O-V-E-R-L-O-R-D/ECE-411-Practicum/3D Model Prototype/Version 4.0/crossesction.png

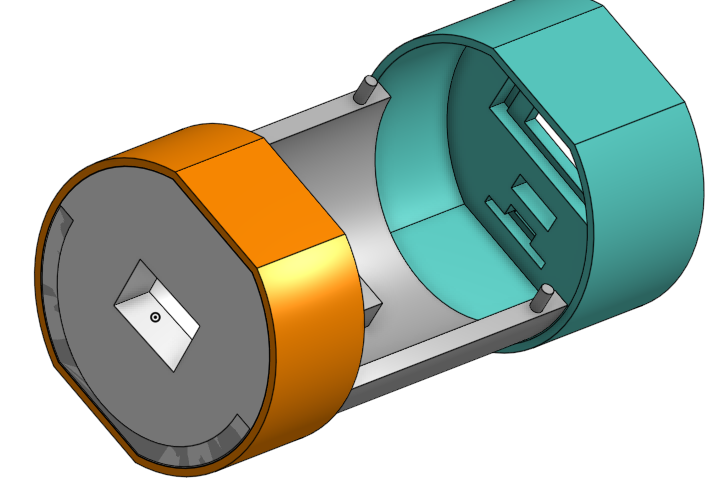
3D Model Prototype/Version 4.0/crossesction.png
