O-V-E-R-L-O-R-D/ECE-411-Practicum/Project Photos/Prototype_Blue_Color.jpg

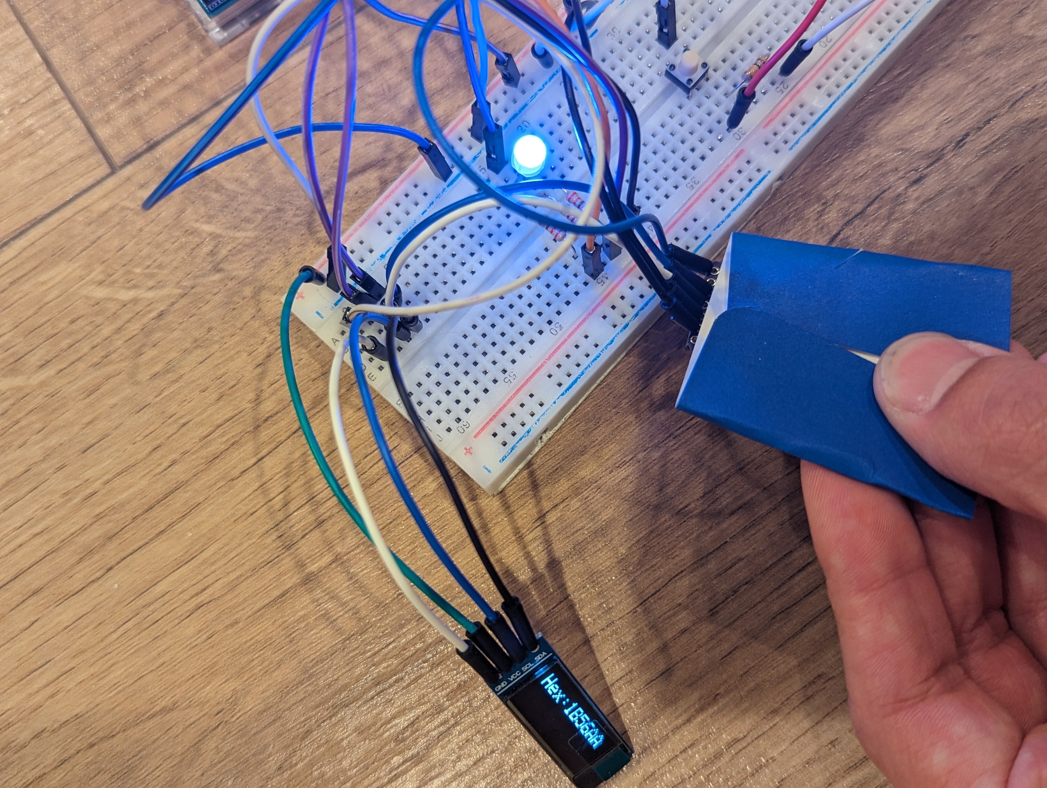
Project Photos/Prototype_Blue_Color.jpg
