O-V-E-R-L-O-R-D/ECE-411-Practicum/Receipt Board Purchase.png

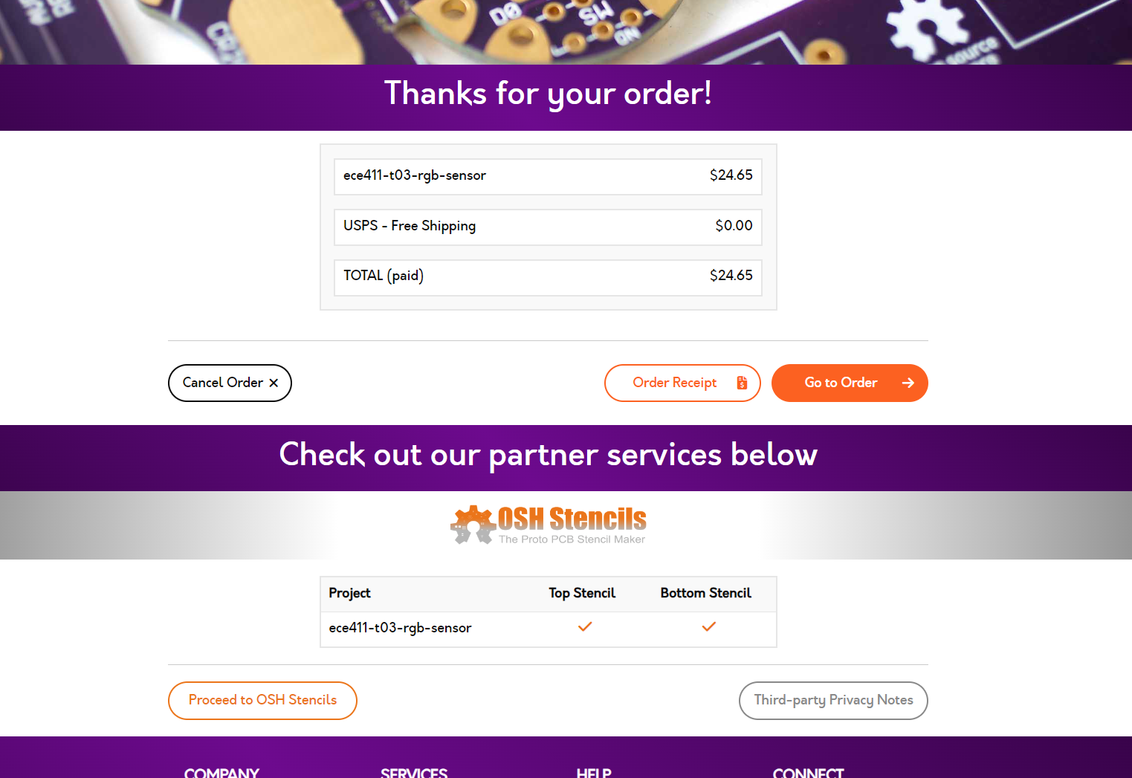
Receipt Board Purchase.png
